NeuroTinker/NeuroBytes_Battery_Pack/HARDWARE/mitochondria_cu.png

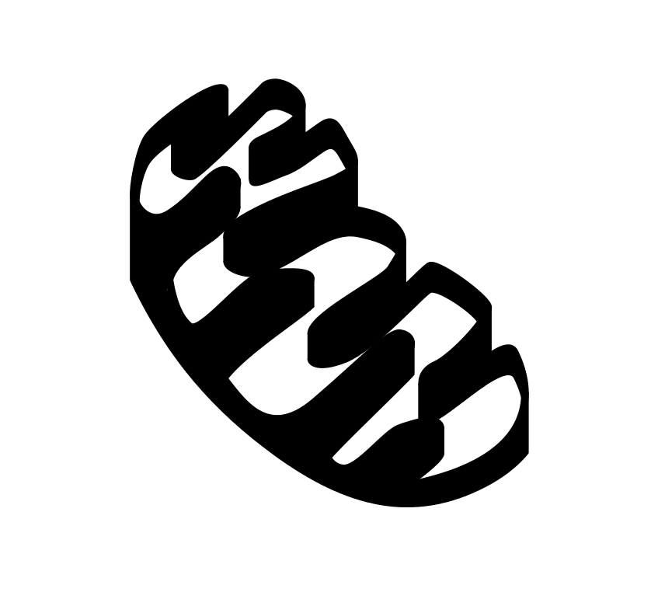
HARDWARE/mitochondria_cu.png
